Gabriele-tomai00/split_keyboard_2_qmk_pcb/images/20251119_160013.jpg

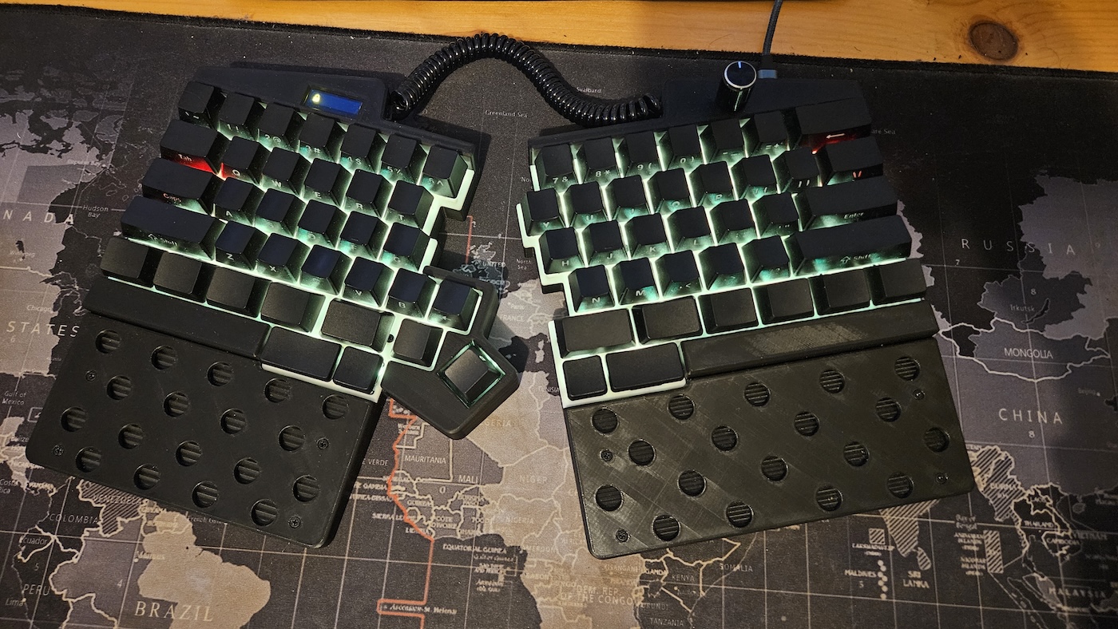
images/20251119_160013.jpg
