Gabriele-tomai00/split_keyboard_2_qmk_pcb/kicad/3d_models/Raspberry_Pi_Pico_micro_usb.step

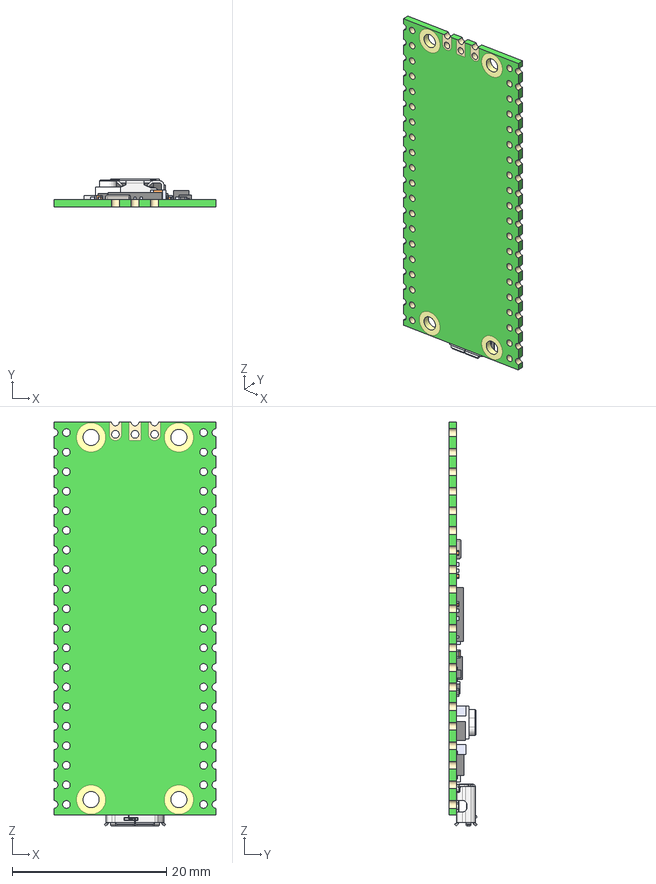
[picture p29: CAD file, 2025-08-09]
kicad/3d_models/Raspberry_Pi_Pico_micro_usb.step
21.0 x 3.69 x 52.4 mm
PCB, Raspberry Pi Pico-R3
MicroUSB Port, Raspberry Pi Pico-R3
RP2040 Microcontroller, Raspberry Pi Pico-R3
SW1, Tact Switch, Raspberry Pi Pico-R3
D1, Diode, Schottky, Raspberry Pi Pico-R3
D2, QSME-C194, LED, Raspberry Pi Pico-R3
L1, Inductor, Raspberry Pi Pico-R3
U2, RT6150B-33GQW, Buck Boost Converter, Raspberry Pi Pico-R3
U3, W25Q16JVUXIQ, Serial NOR Flash 16 Mbit, Raspberry Pi Pico-R3
Q1, MOSFET, DMG1012T, Raspberry Pi Pico-R3
X1, X12M000000S096, 12 Mhz Crystal Resonator, Raspberry Pi Pico-R3
SMD Resistor, Configurable, Raspberry Pi Pico-R3_R1
SMD Resistor, Configurable, Raspberry Pi Pico-R3_R2
SMD Resistor, Configurable, Raspberry Pi Pico-R3_R3
SMD Resistor, Configurable, Raspberry Pi Pico-R3_R4
SMD Resistor, Configurable, Raspberry Pi Pico-R3_R5
SMD Resistor, Configurable, Raspberry Pi Pico-R3_R6
SMD Resistor, Configurable, Raspberry Pi Pico-R3_R7
SMD Resistor, Configurable, Raspberry Pi Pico-R3_R8
SMD Resistor, Configurable, Raspberry Pi Pico-R3_R9
SMD Resistor, Configurable, Raspberry Pi Pico-R3_R10
SMD Resistor, Configurable, Raspberry Pi Pico-R3_R11
SMD Resistor, Configurable, Raspberry Pi Pico-R3_R12
SMD Resistor, Configurable, Raspberry Pi Pico-R3_R13
SMD Resistor, Configurable, Raspberry Pi Pico-R3_R14
SMD Resistor, Configurable, Raspberry Pi Pico-R3_R15
SMD Capacitor, Configurable, Raspberry Pi Pico-R3_C1
SMD Capacitor, Configurable, Raspberry Pi Pico-R3_C2
SMD Capacitor, Configurable, Raspberry Pi Pico-R3_C3
SMD Capacitor, Configurable, Raspberry Pi Pico-R3_C4
SMD Capacitor, Configurable, Raspberry Pi Pico-R3_C5
SMD Capacitor, Configurable, Raspberry Pi Pico-R3_C6
SMD Capacitor, Configurable, Raspberry Pi Pico-R3_C7
SMD Capacitor, Configurable, Raspberry Pi Pico-R3_C8
SMD Capacitor, Configurable, Raspberry Pi Pico-R3_C9
SMD Capacitor, Configurable, Raspberry Pi Pico-R3_C10
SMD Capacitor, Configurable, Raspberry Pi Pico-R3_C11
SMD Capacitor, Configurable, Raspberry Pi Pico-R3_C12
SMD Capacitor, Configurable, Raspberry Pi Pico-R3_C13
SMD Capacitor, Configurable, Raspberry Pi Pico-R3_C14
SMD Capacitor, Configurable, Raspberry Pi Pico-R3_C15
SMD Capacitor, Configurable, Raspberry Pi Pico-R3_C16
SMD Capacitor, Configurable, Raspberry Pi Pico-R3_C17
SMD Capacitor, Configurable, Raspberry Pi Pico-R3_C18
