Gabriele-tomai00/split_keyboard_2_qmk_pcb/3d_models/left_keyboard_part/cover_left.stl

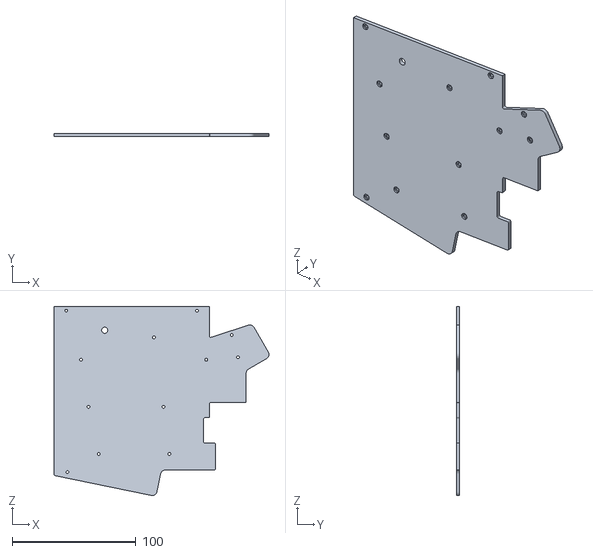
[picture p30: CAD file, 2026-01-29]
3d_models/left_keyboard_part/cover_left.stl
173.8 x 2.80 x 152.8
