Gabriele-tomai00/split_keyboard_2_qmk_pcb/3d_models/right_keyboard_part/cover_right.stl

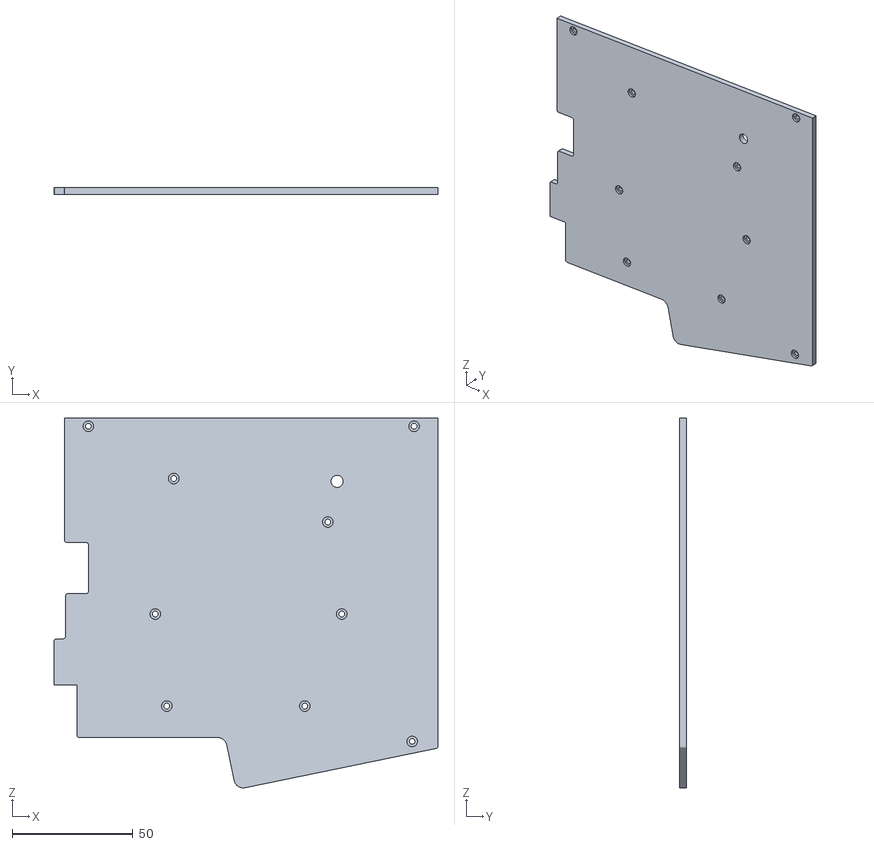
[picture p31: CAD file, 2026-01-29]
3d_models/right_keyboard_part/cover_right.stl
159.0 x 2.80 x 153.1
