Gabriele-tomai00/split_keyboard_2_qmk_pcb/kicad/3d_models/vite_punta_torx.step

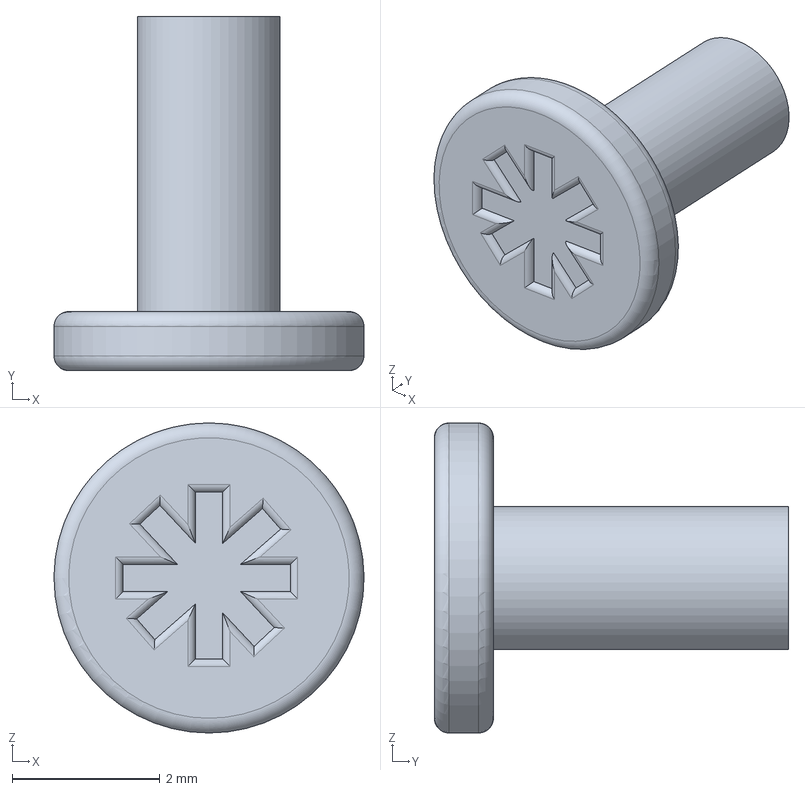
[picture p32: CAD file, 2025-08-09]
kicad/3d_models/vite_punta_torx.step
4.20 x 4.80 x 4.20 mm
