Gabriele-tomai00/split_keyboard_2_qmk_pcb/3d_models/left_keyboard_part/keyboard_left.stl

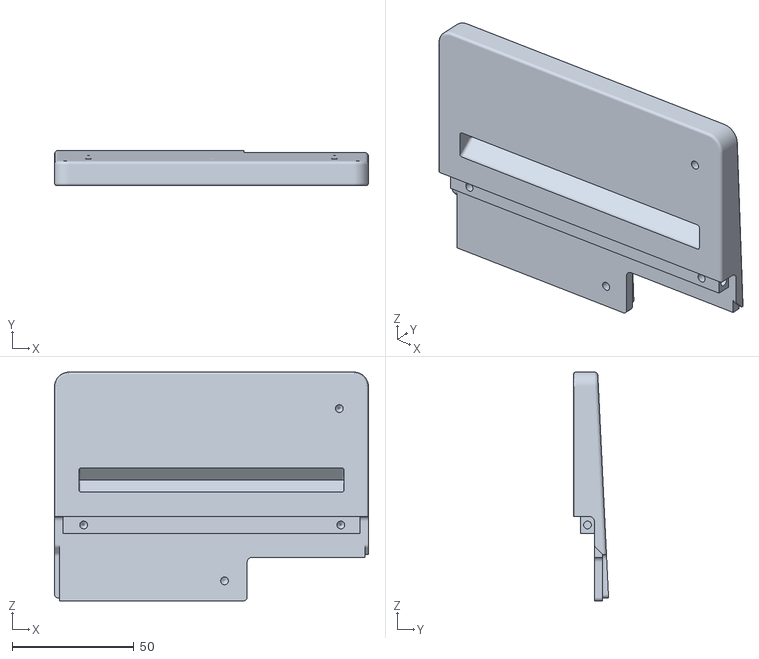
[picture p33: CAD file, 2026-01-29]
3d_models/left_keyboard_part/keyboard_left.stl
129.1 x 14.5 x 94.1
