Gabriele-tomai00/split_keyboard_2_qmk_pcb/3d_models/right_keyboard_part/internal_wall_right.stl

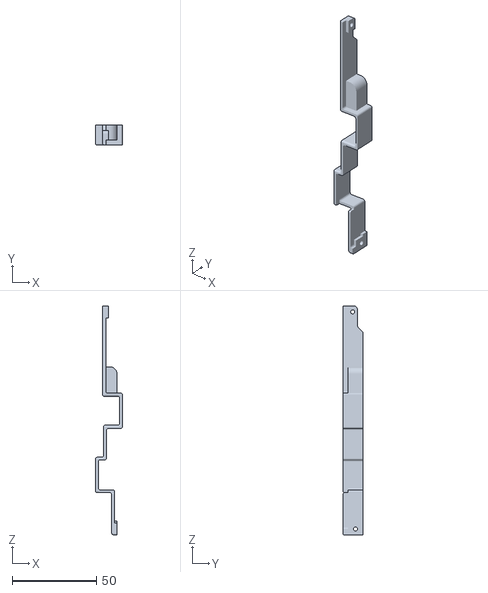
[picture p34: CAD file, 2026-01-29]
3d_models/right_keyboard_part/internal_wall_right.stl
16.1 x 12.0 x 135.9
