Gabriele-tomai00/split_keyboard_2_qmk_pcb/3d_models/left_keyboard_part/upper_left.stl

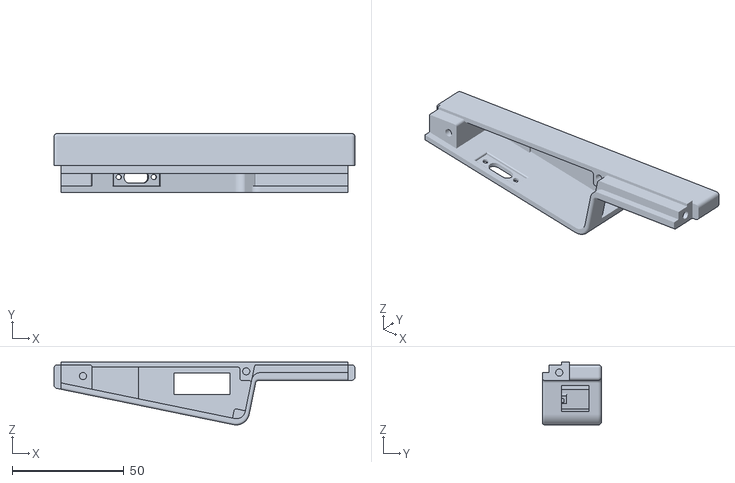
[picture p36: CAD file, 2026-01-29]
3d_models/left_keyboard_part/upper_left.stl
134.5 x 26.4 x 28.1
