Gabriele-tomai00/split_keyboard_2_qmk_pcb/3d_models/right_keyboard_part/keyboard_right.stl

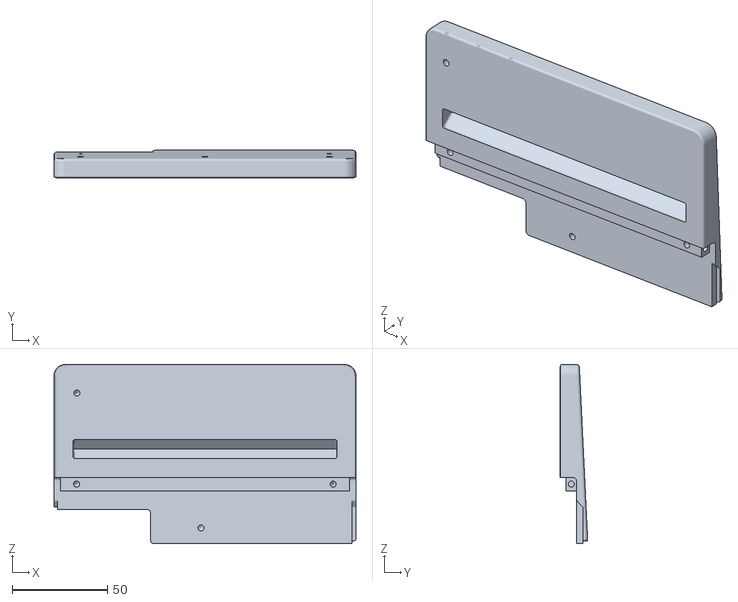
[picture p37: CAD file, 2026-01-29]
3d_models/right_keyboard_part/keyboard_right.stl
158.7 x 14.5 x 94.1
