Gabriele-tomai00/split_keyboard_2_qmk_pcb/3d_models/left_keyboard_part/palm_rest_left.stl

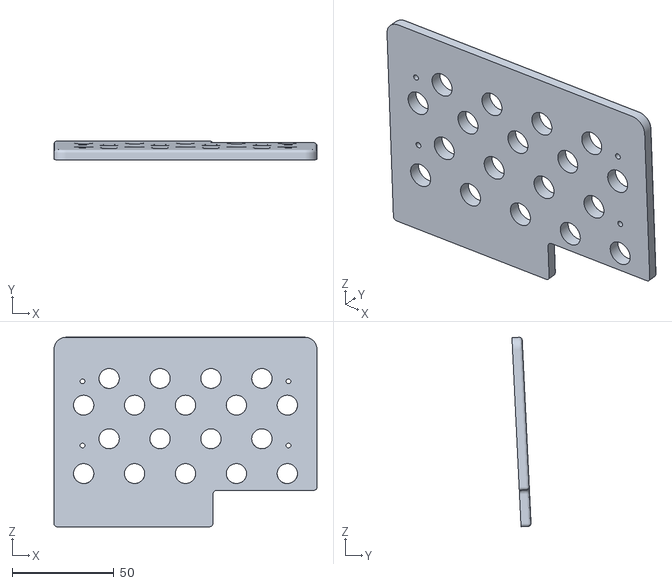
[picture p39: CAD file, 2026-01-29]
3d_models/left_keyboard_part/palm_rest_left.stl
129.1 x 9.38 x 93.1
