Gabriele-tomai00/split_keyboard_2_qmk_pcb/kicad/3d_models/RJ11_CONNECTOR.step

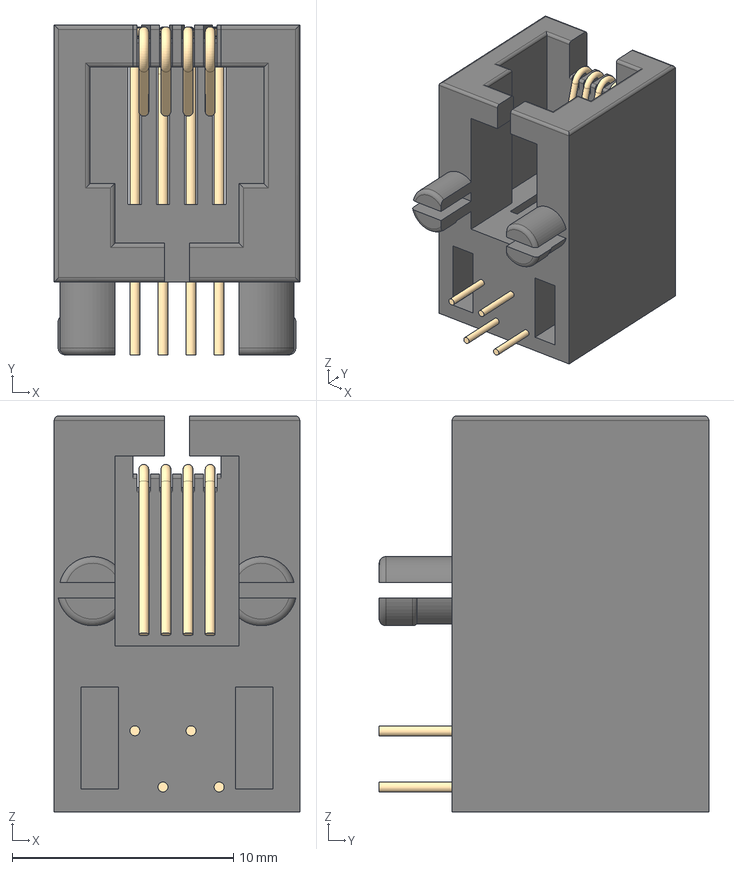
[picture p40: CAD file, 2025-08-09]
kicad/3d_models/RJ11_CONNECTOR.step
11.1 x 14.9 x 17.9 mm
