Gabriele-tomai00/split_keyboard_2_qmk_pcb/kicad/3d_models/encoder_ALPS.step

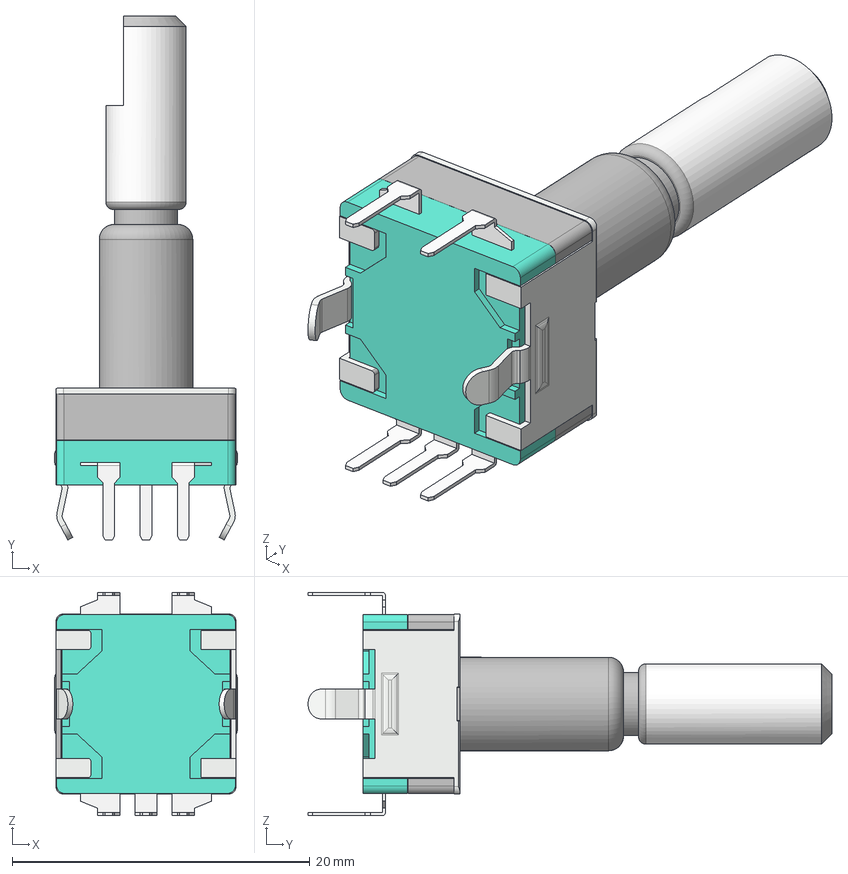
[picture p41: CAD file, 2025-08-09]
kicad/3d_models/encoder_ALPS.step
12.3 x 35.2 x 15.0 mm
