Gabriele-tomai00/split_keyboard_2_qmk_pcb/kicad/3d_models/cilindro_4mm.step

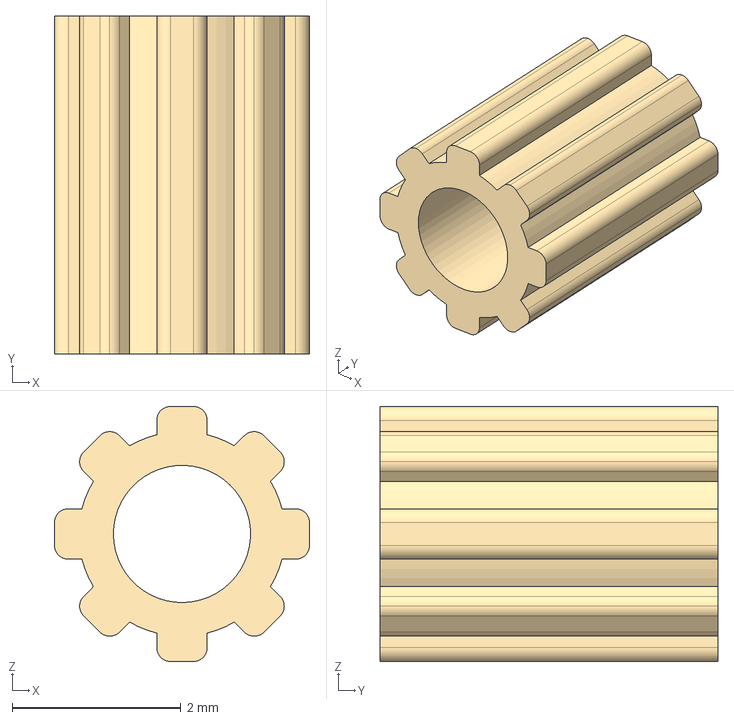
[picture p43: CAD file, 2025-08-09]
kicad/3d_models/cilindro_4mm.step
3.02 x 4.00 x 3.02 mm
