Gabriele-tomai00/split_keyboard_2_qmk_pcb/kicad/3d_models/OLED_128x32.step

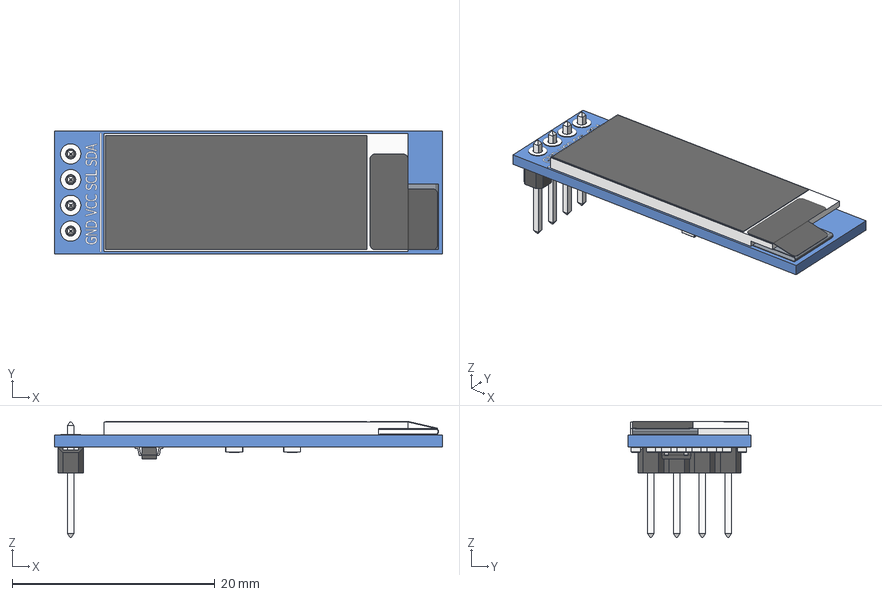
[picture p44: CAD file, 2025-08-09]
kicad/3d_models/OLED_128x32.step
38.3 x 12.1 x 11.5 mm
OLED_0.91_128x32
Pin Header 4 x 1 TH 2.54mm Pitch
RESC-0603 x 13
2SD0601A
